mak3r/steer-case/tests/switch-top.stl

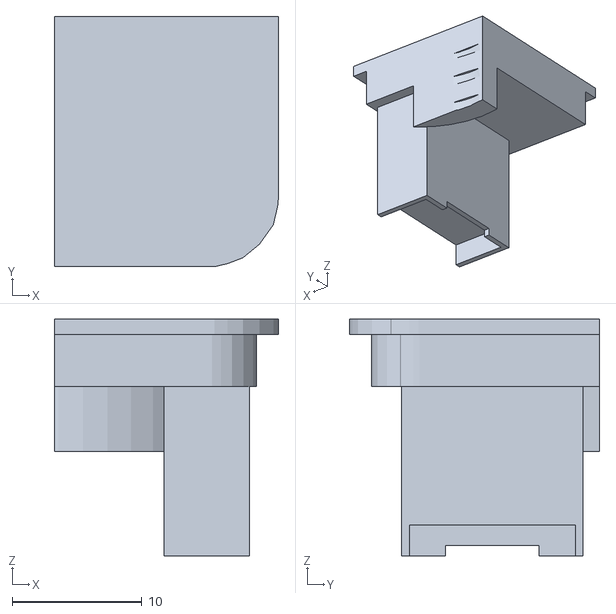
[picture p16: CAD file, 2019-03-14]
tests/switch-top.stl
17.3 x 19.3 x 18.2
