mak3r/steer-case/tests/part.stl

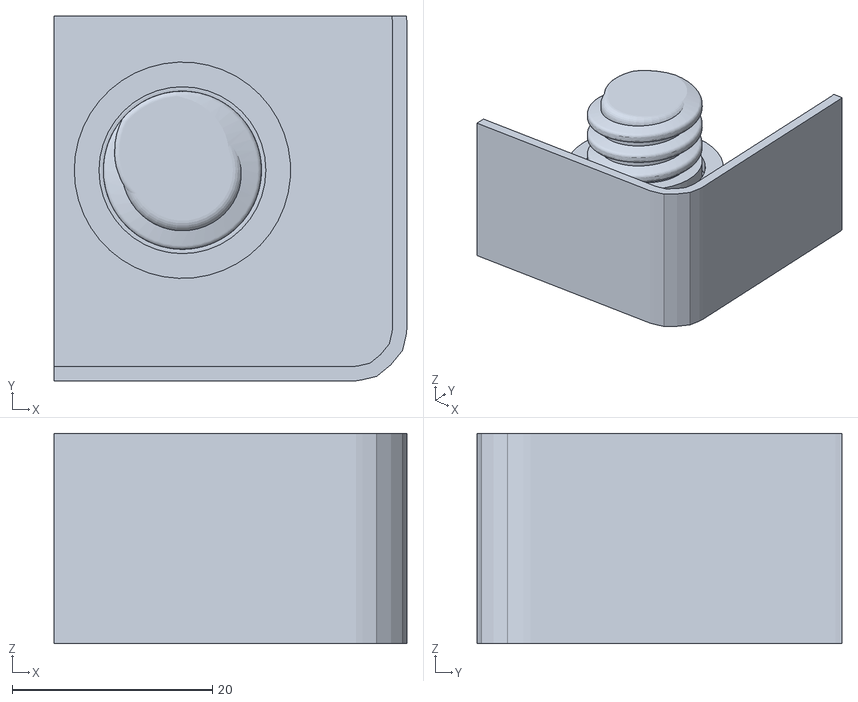
[picture p17: CAD file, 2019-03-14]
tests/part.stl
35.2 x 36.4 x 21.0
