mak3r/steer-case/tests/light-pipes-top.stl

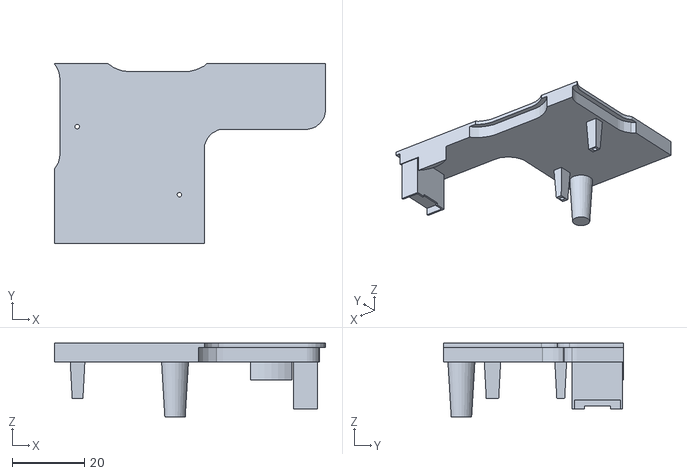
[picture p18: CAD file, 2019-03-14]
tests/light-pipes-top.stl
75.3 x 50.0 x 20.5
