mak3r/steer-case/tests/switch-base.stl

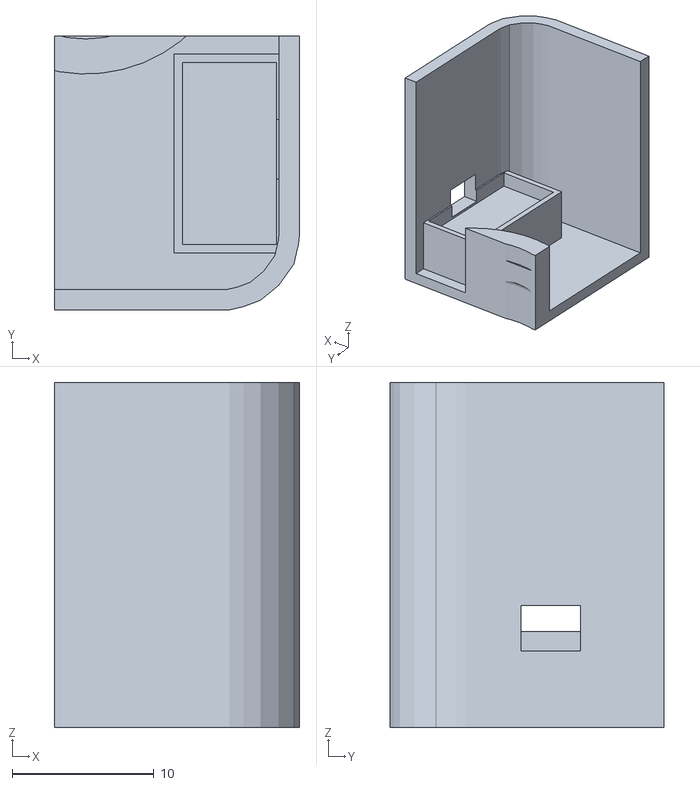
[picture p19: CAD file, 2019-03-14]
tests/switch-base.stl
17.3 x 19.3 x 24.3
