mak3r/steer-case/tests/part.scad

difference() {
difference() {
import("cattle-pi-BaseSampleComponents-v23.stl");
translate([-45,-20,-5])
cube([120,185,30]);
}
#translate([-68,-97,-5])
cube([100,230,30]);
}
